serisman/HIDman-mini/KiCad PCBs/DB9-to-TTL/output/3D Bottom.png

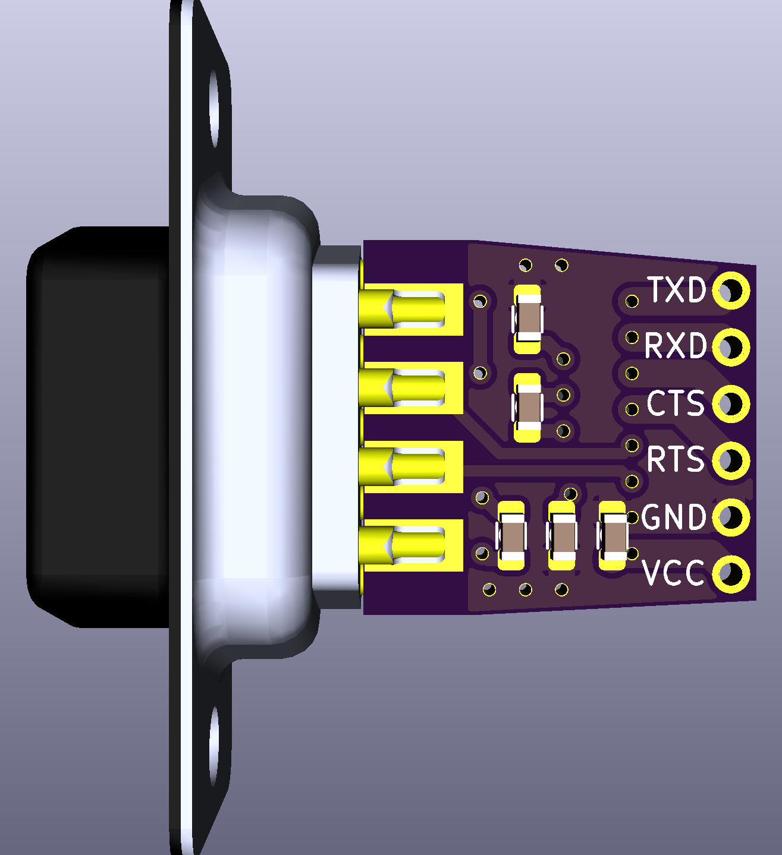
KiCad PCBs/DB9-to-TTL/output/3D Bottom.png
