serisman/HIDman-mini/KiCad PCBs/DB9-to-TTL/output/OSHPARK Bottom.png

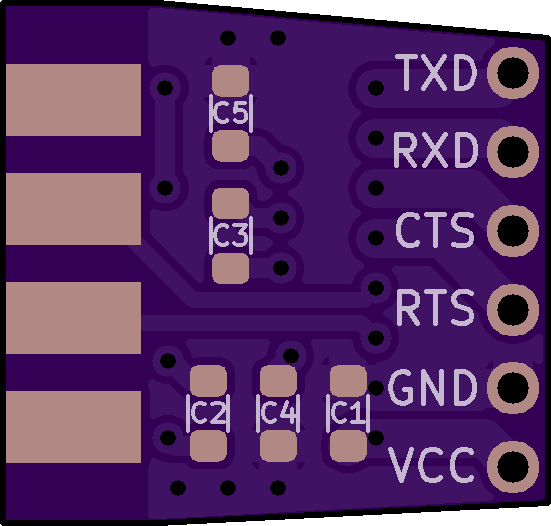
KiCad PCBs/DB9-to-TTL/output/OSHPARK Bottom.png
