serisman/HIDman-mini/KiCad PCBs/DB9-to-TTL/output/OSHPARK Top.png

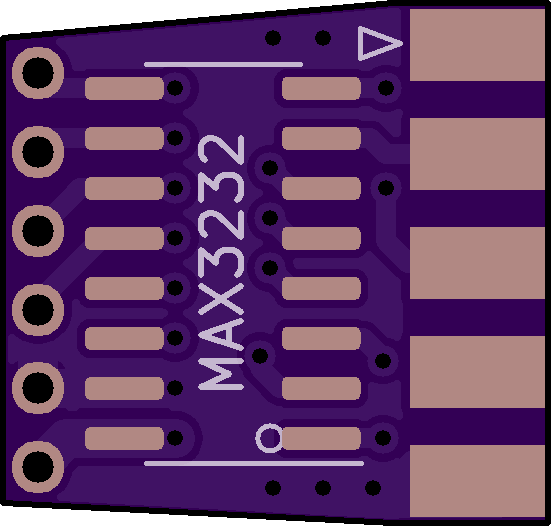
KiCad PCBs/DB9-to-TTL/output/OSHPARK Top.png
