serisman/HIDman-mini/pictures/HIDman-micro/Compared to HIDman-mini.jpg

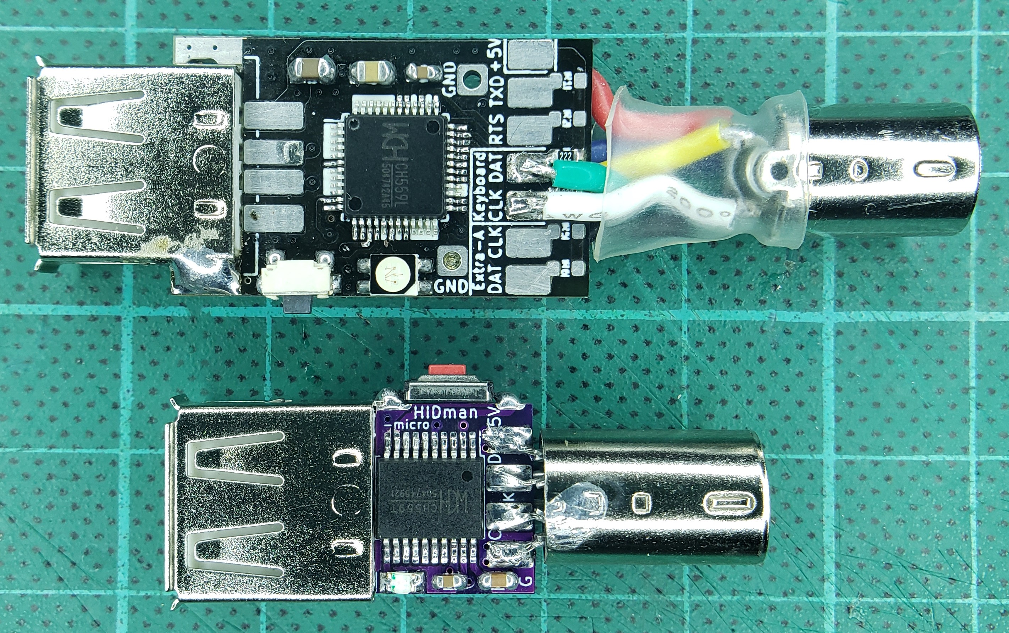
pictures/HIDman-micro/Compared to HIDman-mini.jpg
